lambdakb/keyboard-lk23m/output/case/fr4/img/lk23m-bottom-bottom.png

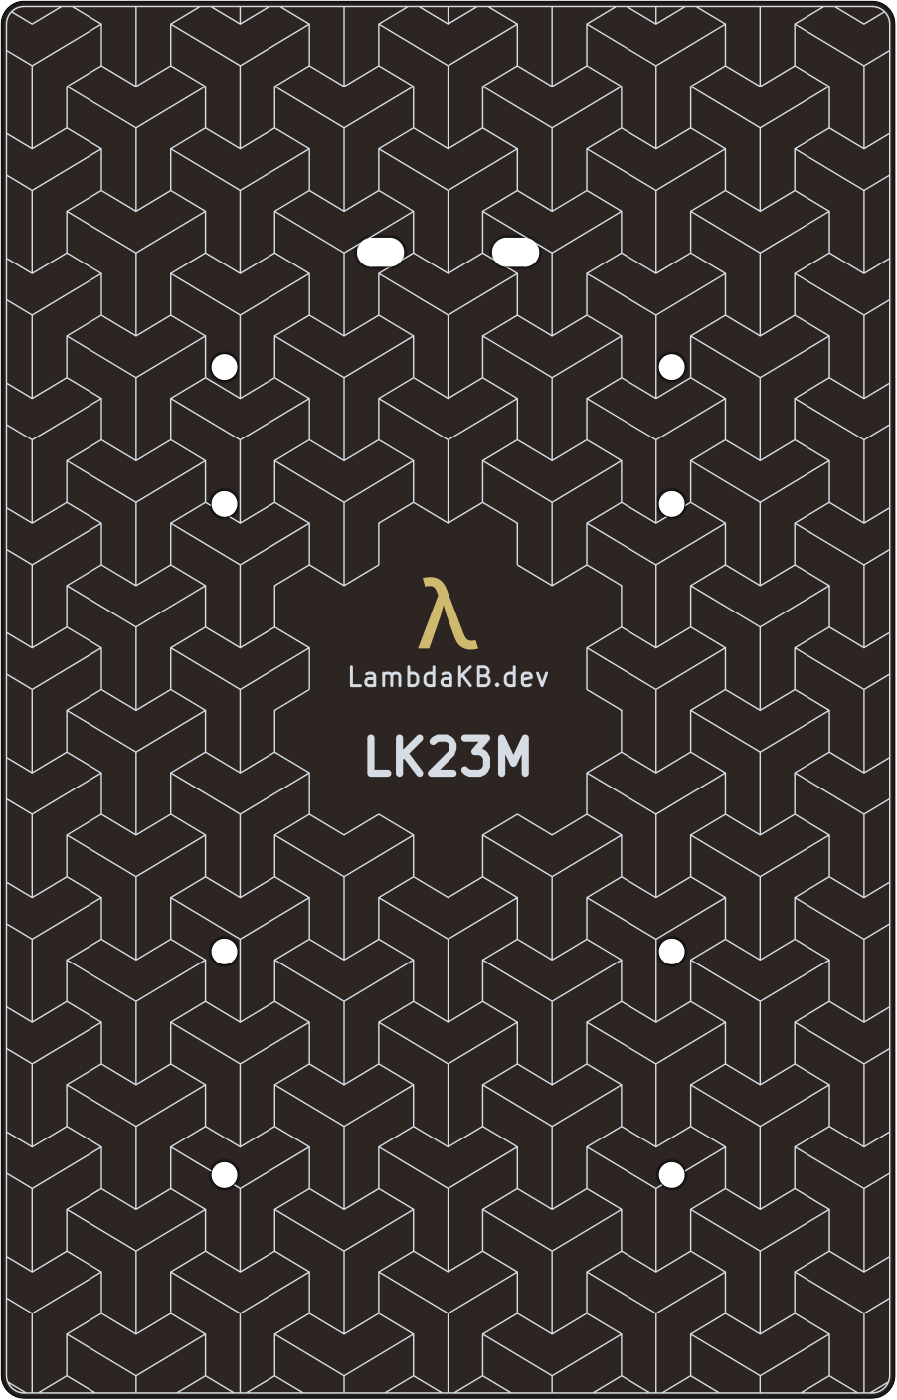
output/case/fr4/img/lk23m-bottom-bottom.png
