lambdakb/keyboard-lk23m/output/case/fr4/img/lk23m-bottom-top.png

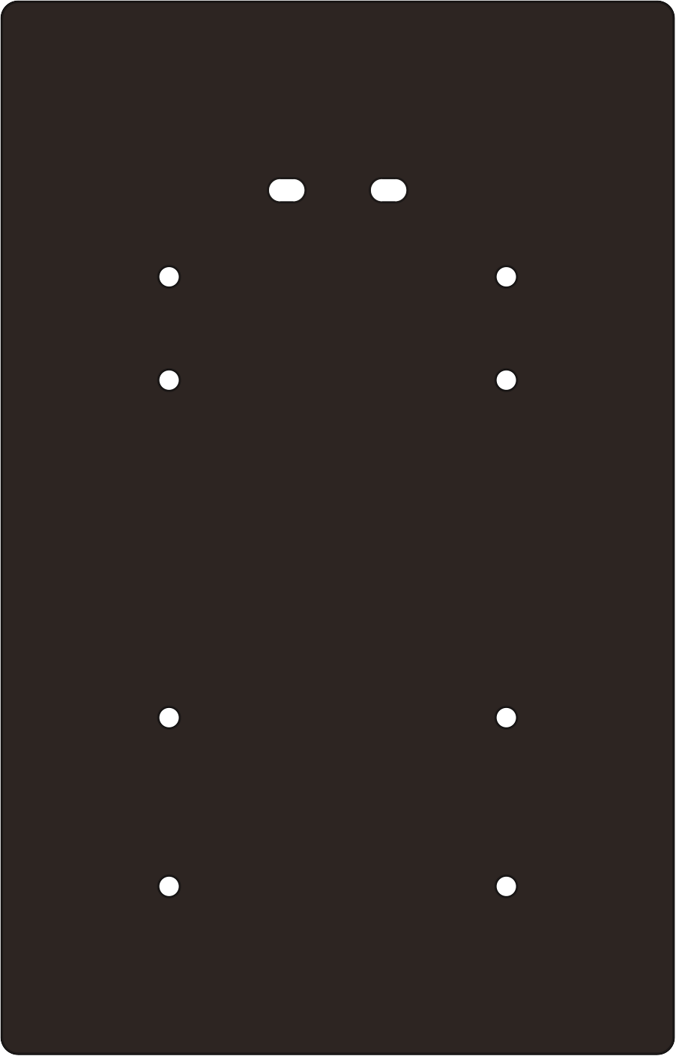
output/case/fr4/img/lk23m-bottom-top.png
