lambdakb/keyboard-lk23m/output/pcb/img/lk23m-pcb-bottom.png

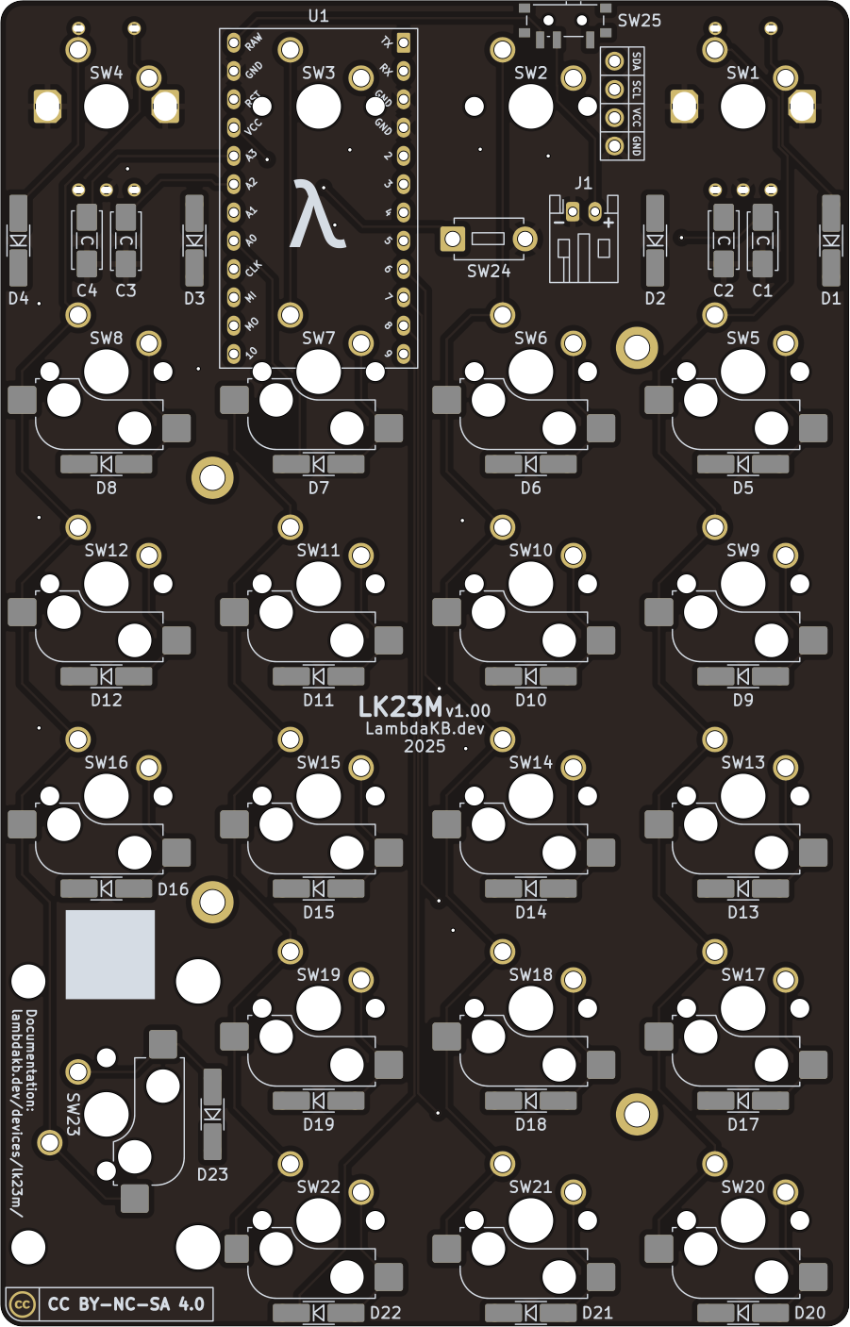
output/pcb/img/lk23m-pcb-bottom.png
