lambdakb/keyboard-lk23m/output/pcb/img/lk23m-pcb-top.png

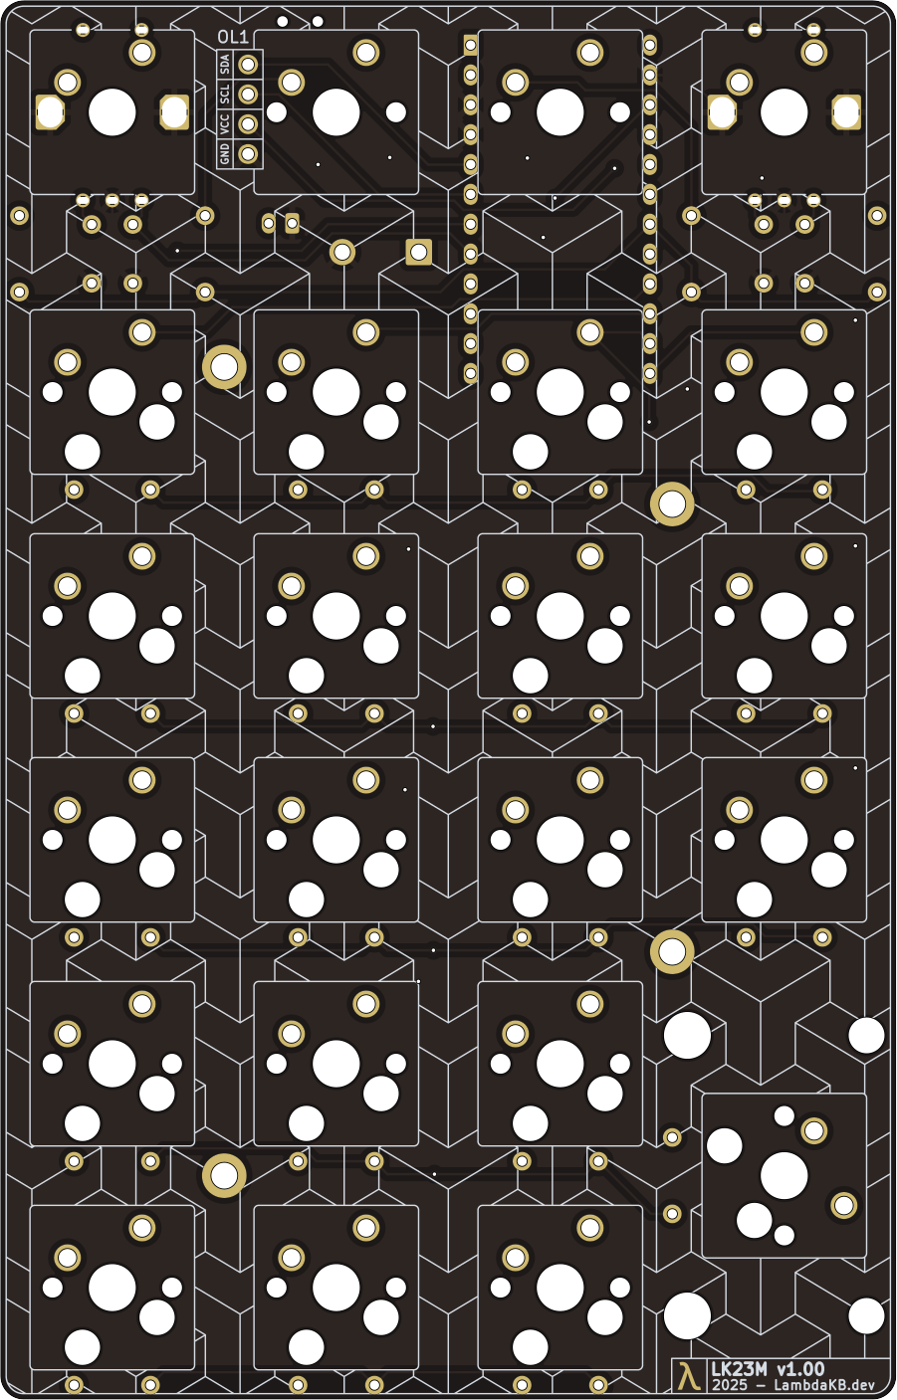
output/pcb/img/lk23m-pcb-top.png
